dunceworks/FAST-AR/py/test_images/afghan.png

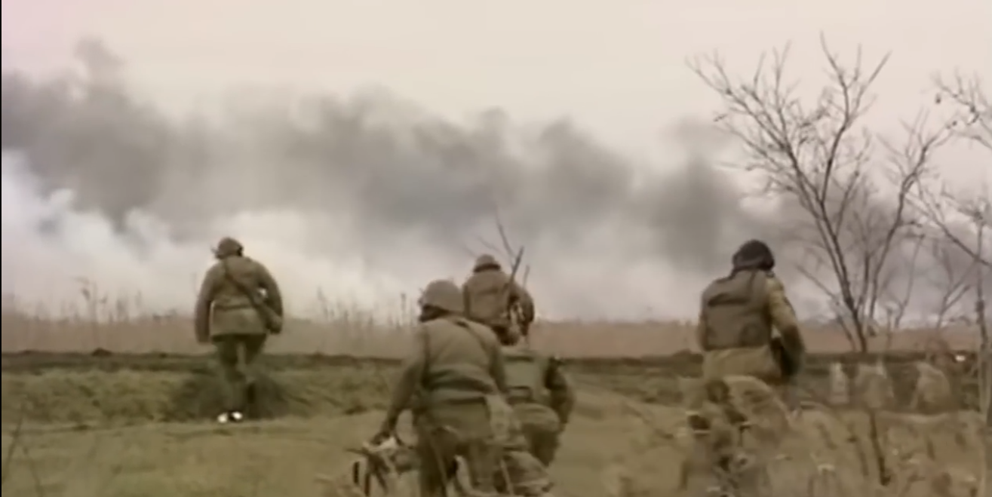
py/test_images/afghan.png
