dunceworks/FAST-AR/py/test_images/image.png

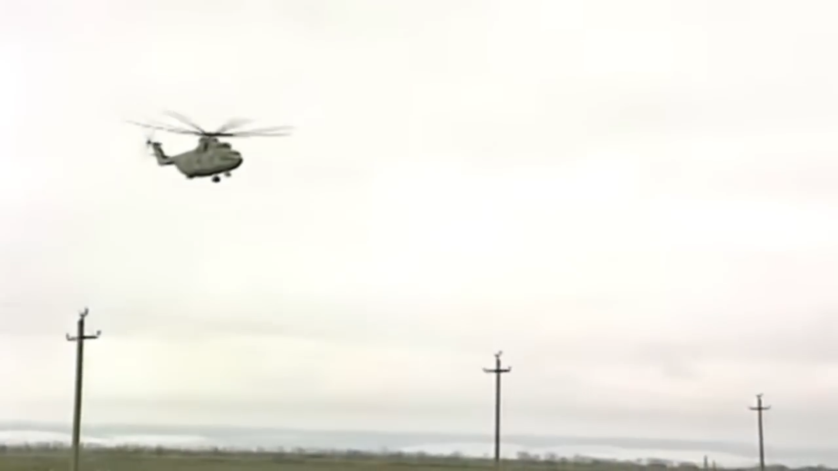
py/test_images/image.png
