dunceworks/FAST-AR/py/test_images/sc2.png

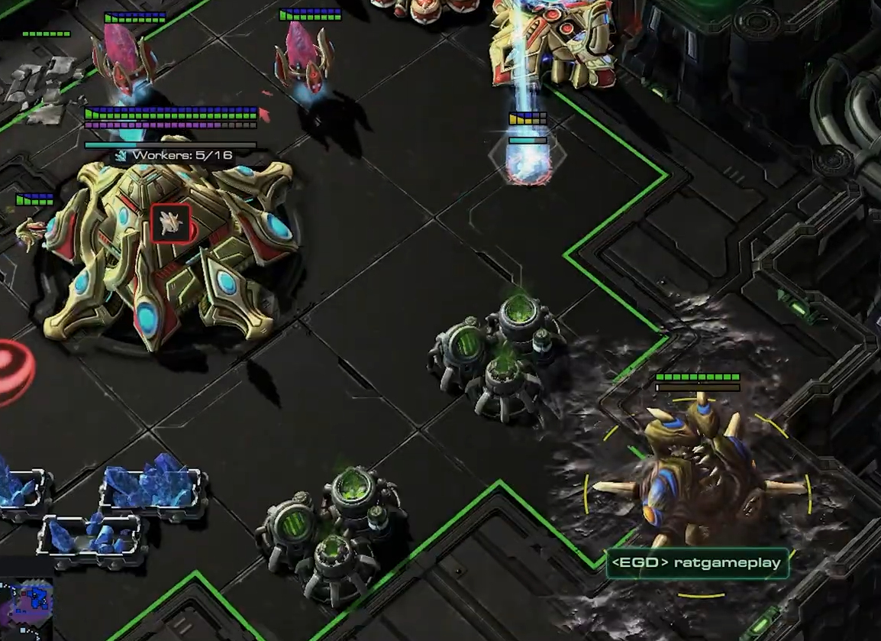
py/test_images/sc2.png
