dunceworks/FAST-AR/py/test_img_gen/input_img/camel_1080p.png

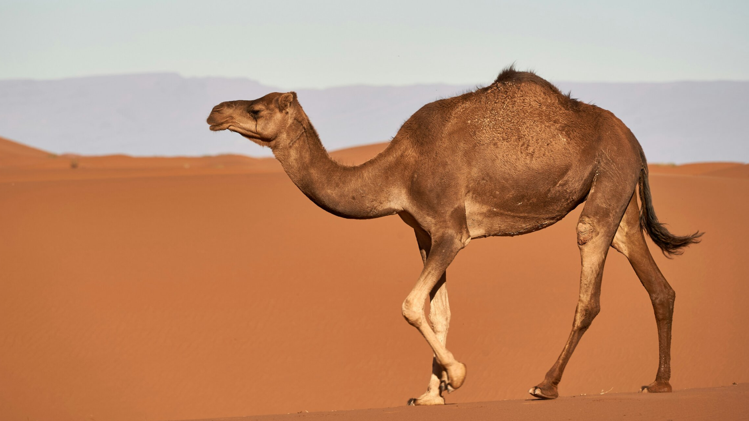
py/test_img_gen/input_img/camel_1080p.png
