dunceworks/FAST-AR/py/test_img_gen/input_img/Compass.png

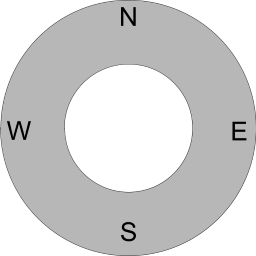
py/test_img_gen/input_img/Compass.png
