dunceworks/FAST-AR/py/test_img_gen/output_img/compass.png

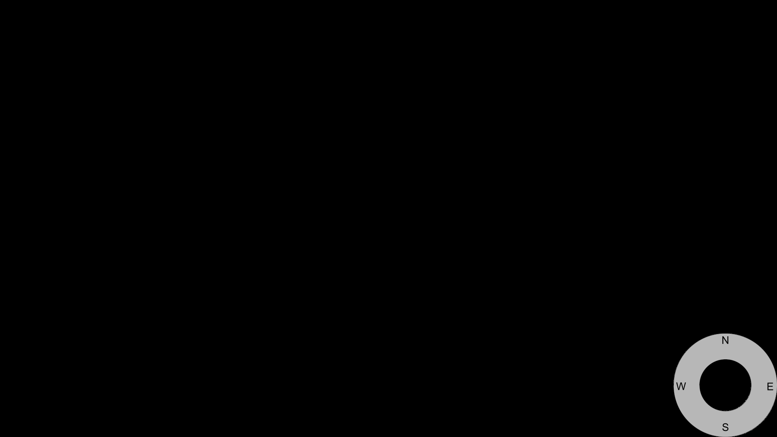
py/test_img_gen/output_img/compass.png
