dunceworks/FAST-AR/py/test_img_gen/output_img/crop_image_camel.png

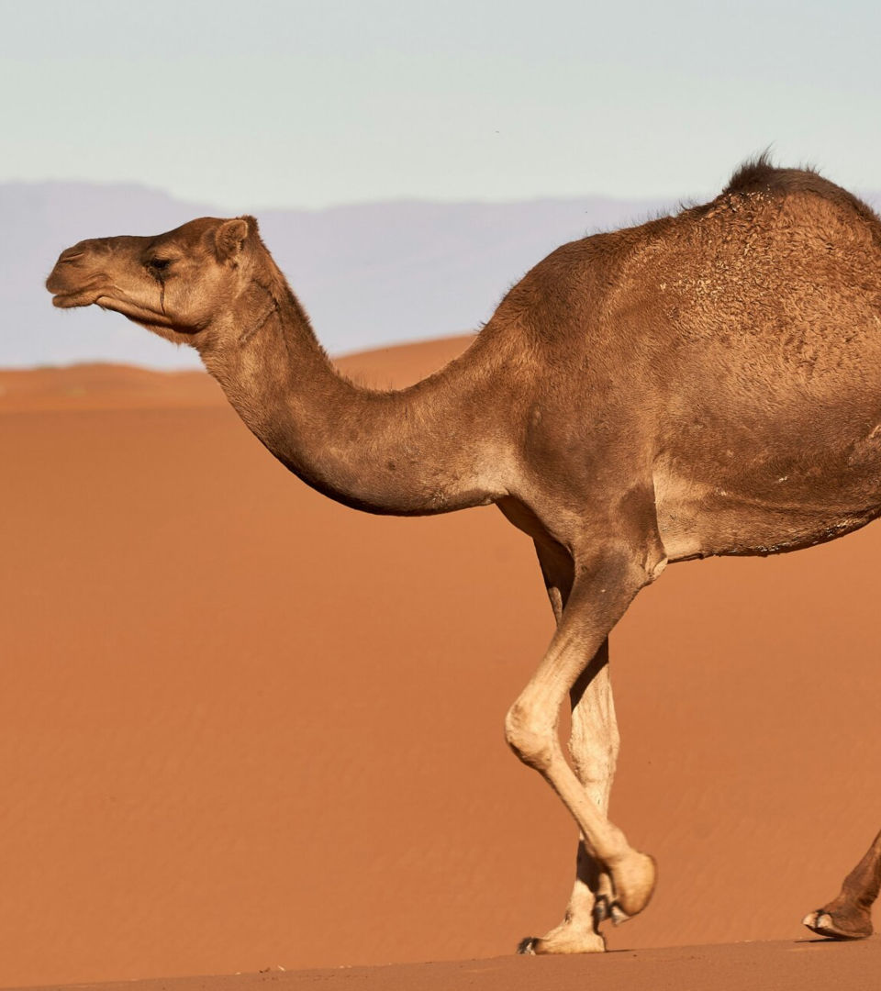
py/test_img_gen/output_img/crop_image_camel.png
