dunceworks/FAST-AR/py/test_img_gen/output_img/downscaler_param.png

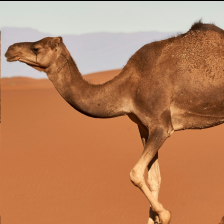
py/test_img_gen/output_img/downscaler_param.png
