dunceworks/FAST-AR/py/test_img_gen/output_img/frame_pipeline_WHOLE_output_stitch_camel.png

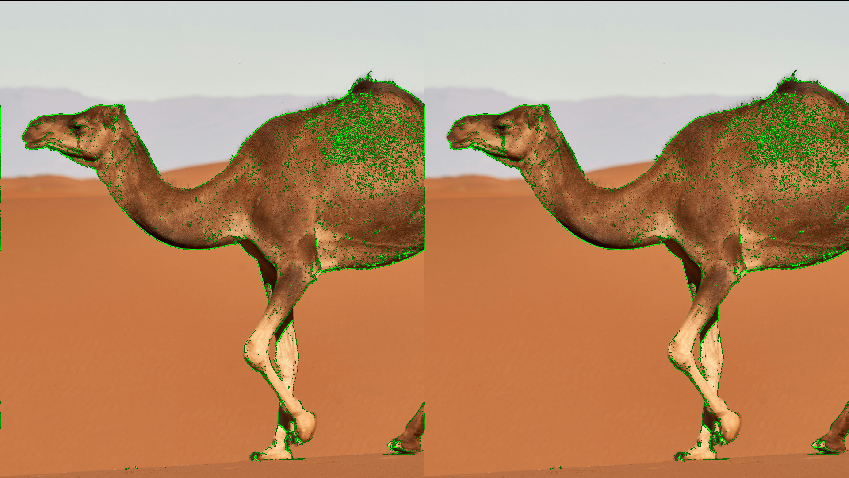
py/test_img_gen/output_img/frame_pipeline_WHOLE_output_stitch_camel.png
