dunceworks/FAST-AR/IP/AXI_Stream_bound_box/src/AXI4-Stream_bounding_box.sv.sv

///////////////////////////////////////////////////////// 
//
// File name: AXI4-Stream_bounding_box.sv
// 
// Description: Wrapper for the bounding box module using AXI4-Stream interface
//
// Created  : 2026-04-20
// Modified : 2026-04-20 nice
// Author   : Wysong
//
// Team     : Dunce Works
//
// AI Disclosure: This is a wrapper. Hopefully that says enough :P
//
// Written?     [X]
// SW Tested?   [X]
// HW Tested?   [ ]
//
////////////////////////////////////////////////////////


module AXI4_Stream_bounding_box #(
    parameter DS_FACTOR = 4,    // DS_FACTOR and DOWNSCALE_SIZE should reflect options chosen in the dowsncale module.
    parameter DOWNSCALE_SIZE = 224,
    parameter LINE_WIDTH = 10, // Thickness of the bounding box lines in pixels
    parameter INPUT_WIDTH = 1920,
    parameter INPUT_HEIGHT = 1080
)(
    input wire aclk,
    input wire aresetn,

// Standard Xilinx Naming for Slave (Input)
    input  wire               s_axis_tvalid,
    input  wire        [23:0] s_axis_tdata,
    input  wire               s_axis_tlast,
    input  wire               s_axis_tuser,
    output wire               s_axis_tready,
    
    // Standard Xilinx Naming for Master (Output)
    output wire               m_axis_tvalid,
    output wire        [23:0] m_axis_tdata,
    output wire               m_axis_tlast,
    output wire               m_axis_tuser,
    input  wire               m_axis_tready
);

    axi4s_vid_if axi4s_in();
    axi4s_vid_if axi4s_out();

    // Just flattening so that vivado stops throwing fits at me
    // when packaging IP... maybe a lot more of these to come.
    assign axi4s_in.tvalid = s_axis_tvalid;
    assign axi4s_in.tdata  = s_axis_tdata;
    assign axi4s_in.tlast  = s_axis_tlast;
    assign axi4s_in.tuser  = s_axis_tuser;
    assign s_axis_tready   = axi4s_in.tready;

    assign m_axis_tvalid   = axi4s_out.tvalid;
    assign m_axis_tdata    = axi4s_out.tdata;
    assign m_axis_tlast    = axi4s_out.tlast;
    assign m_axis_tuser    = axi4s_out.tuser;
    assign axi4s_out.tready= m_axis_tready;

    // Instantiate the module and hook it up.
    // make sure to expose parameters in the wrapper as well.

    bounding_box #(
        .DS_FACTOR(DS_FACTOR),
        .DOWNSCALE_SIZE(DOWNSCALE_SIZE),
        .LINE_WIDTH(LINE_WIDTH),
        .INPUT_WIDTH(INPUT_WIDTH),
        .INPUT_HEIGHT(INPUT_HEIGHT)
    ) bounding_box_inst (
        .aclk(aclk),
        .areset_n(aresetn),
        .axi4s_in(axi4s_in),
        .axi4s_out(axi4s_out)
    );

endmodule
